AndrewPasco/me327-proj/controllerTest/controllerTest/src/BeltIMU.cpp

#include "BeltIMU.h"

BeltIMU::BeltIMU() :
    bno08x(-1),
    oldQuat{1,0,0,0}
{
    return;
}

BeltIMU::~BeltIMU(){}

// pass the quaternion you want the device to consider as
// its initial orientation, relative to lying flat (probably)
// just set to 1,0,0,0 and then orient it how you want, print the
// quaternion, and pass that
void BeltIMU::setup(Quat initialOrientation){
    initQ = Qnormalize(initialOrientation);
    oldQuat = initQ;

    if (!bno08x.begin_I2C()) {
        Serial.println("Failed to find BNO08x chip");
        return;
    }
    connected = true;
    set_reports();
    Serial.println("Reading IMU events");
}

bool BeltIMU::check_connection() {
    // re attemp connectino if not connected
    if (!connected) {
        if (!bno08x.begin_I2C()) {
            Serial.println("Failed to find BNO08x chip");
            return false;
        }
        connected = true;
    }

    // reset reports if device was reset
    if (bno08x.wasReset()) {
        Serial.print("IMU was reset, attempting to set reports ");
        justReset = true;
        bool reEnabled = set_reports();
        return reEnabled;
    }
    return true;
}

Quat BeltIMU::get_quaternion () {
    if (!connected) {
        Serial.println("IMU not connected");
        return oldQuat;
    }

    // retrieve quaternion from IMU. It will always be oriented assuming
    // initial position is board lying flat down
    sh2_SensorValue_t data;
    if (!bno08x.getSensorEvent(&data)) {
        // No new data available this loop iteration
        return oldQuat;
    }
    float qw = data.un.rotationVector.real;
    float qx = data.un.rotationVector.i;
    float qy = data.un.rotationVector.j;
    float qz = data.un.rotationVector.k;
    Quat newQuat{qw,qx,qy,qz};

    // rotate quaternion by opposite of initial orientation quaternion
    // to find quaternion relative to initial orientation
    Quat reorientedQuat = Qmultiply( newQuat, Qconj(initQ) );
    
    // if (justReset) {
    //     // Find offsetQ such that Qmultiply(reorientedQuat, offsetQ) == oldQuat
    //     // offsetQ = Qmultiply(Qconj(reorientedQuat), oldQuat)
    //     offsetQ = Qmultiply(Qconj(reorientedQuat), oldQuat);
    //     justReset = false;
    // }
    
    // Apply offset
    Quat finalQuat = Qmultiply(reorientedQuat, offsetQ);
    
    oldQuat = finalQuat;

    return finalQuat;
}

float BeltIMU::get_heading() {
    // get latest quaternion
    Quat q = get_quaternion();
    // Convert to Euler Yaw (heading)
    // using standard formula
    float siny_cosp = 2.0f * (q.w * q.z + q.x * q.y);
    float cosy_cosp = 1.0f - 2.0f * (q.y * q.y + q.z * q.z);
    float yaw_rad = atan2(siny_cosp, cosy_cosp);
    float yaw_deg = yaw_rad * 180.0f / M_PI;
    return yaw_deg;
}


/****************
 Private
*****************/
bool BeltIMU::set_reports() {
    if (!connected) {
        return false;
    }
    Serial.println("Setting desired reports");
    if (! bno08x.enableReport(SH2_GAME_ROTATION_VECTOR)) {
        Serial.println("Could not enable game vector");
        return false;
    }
    return true;
}

/****************
 Quaternion Stuff
*****************/
Quat Qmultiply(const Quat& a, const Quat& b) {
    float qw = a.w*b.w - a.x*b.x - a.y*b.y - a.z*b.z;
    float qx = a.w*b.x + a.x*b.w + a.y*b.z - a.z*b.y;
    float qy = a.w*b.y - a.x*b.z + a.y*b.w + a.z*b.x;
    float qz = a.w*b.z + a.x*b.y - a.y*b.x + a.z*b.w;
    
    Quat qnew{qw, qx, qy, qz};
    return Qnormalize(qnew);
}

Quat Qconj(const Quat& q) {
    return {q.w, -q.x, -q.y, -q.z};
}

Quat Qnormalize(Quat q) {
    float n = sqrt(q.w*q.w + q.x*q.x + q.y*q.y + q.z*q.z);
    return {q.w/n, q.x/n, q.y/n, q.z/n};
}

void printQuat(Quat q) {
    Serial.print("qw:");
    Serial.print(q.w);
    Serial.print(" qx:");
    Serial.print(q.x);
    Serial.print(" qy:");
    Serial.print(q.y);
    Serial.print(" qz:");
    Serial.print(q.z);
    Serial.println("");
}
