AndrewPasco/me327-proj/controllerTest/controllerTest/src/ThreatTracker.h

#pragma once
#include "Particle.h"
#include "HapticSignature.h"


struct Threat {
    int id = -1;
    bool active = false;
    float coords[3] = {0,0,0};
    HapticSignature signature;
};
class ThreatTracker
{
public:
    ThreatTracker();
    ~ThreatTracker(){};

    // parses the received byteString into the Threats array
    void update();

    // populates activeList with pointers to active threats
    int getActiveThreats(Threat* activeList[], int maxListSize);

    // calculates relative position of all threats and calls motor driver to
    // appropriately render positions of threats
    void render_threats(const float (&quat)[4]){};

    // callback function to pass to BLE handler
    static void rx_callback( const uint8_t* data,  
							size_t len,  
							const BlePeerDevice& peer,  
							void* context);


private:
    // used to lock thread to allow safe read/write of shared data
    Mutex dataMutex;
    
    static const int maxThreats = 10;
    Threat Threats[maxThreats];
    
    static const size_t messageBufferSize = 10;
    String byteStringBuffer[messageBufferSize];
    size_t messageCount = 0;


	void handle_rx(const uint8_t* data,  
					size_t len,  
					const BlePeerDevice& peer);
	
};
