AndrewPasco/me327-proj/controllerTest/controllerTest/src/BeltIMU.h

#pragma once
#include  "Adafruit_BNO08x_Sahagun.h"

// implementation at end of cpp file
struct Quat {
    float w, x, y, z;
};
Quat Qmultiply(const Quat& a, const Quat& b);
Quat Qconj(const Quat& q);
Quat Qnormalize(Quat q);
void printQuat(Quat q);


class BeltIMU
{
public:
    BeltIMU();
    ~BeltIMU();

    void setup(Quat initialOrientation = {1,0,0,0});

    bool check_connection();

    Quat get_quaternion ();
    float get_heading();
    
private:
    Adafruit_BNO08x bno08x;
    Quat oldQuat;
    Quat initQ;
    Quat offsetQ = {1,0,0,0};

    bool connected = false;
    bool justReset = false;

    bool set_reports();

};
