AndrewPasco/me327-proj/v_env/gui_single.py

# written by Ashlynn as the start of the GUI for the project. 
# This is a simple visualization of the user's heading and the threat location, and it sends motor commands based on the relative angle between the user and the threat. 
# The user can click to set the threat location and use the A/D keys to rotate their heading.
# This script only supports a single threat.

# runs on python 3.11 with pygame, pyserial, numpy, scipy, filterpy, bleak, bluetooth, bluez, bluez-tools

import pygame
import math
# import serial
import time
# BT imports
import asyncio
from bleak import BleakClient, BleakScanner
import threading

# ------------------
# CONFIG
# ------------------

WIDTH = 800
HEIGHT = 800

CENTER = (WIDTH // 2, HEIGHT // 2)

THREAT_X = 500
THREAT_Y = 300

user_heading_deg = 0
latest_heading = 0

NUM_MOTORS = 8
SECTOR_SIZE = 360 / NUM_MOTORS

# For serial
# ser = serial.Serial("/dev/ttyUSB0", 115200)

# For BLE
BLE_ADDRESS = "e8:9f:6d:f2:2c:08"   # MAC address of the Particle Argon
# BLE_ADDRESS = "XX:XX:XX:XX:XX:XX"  # replace with device's MAC address
# BLE_CHARACTERISTIC_UUID = "XXXXXXXX-XXXX-XXXX-XXXX-XXXXXXXXXXXX"  # replace with characteristic UUID

pygame.init()
screen = pygame.display.set_mode((WIDTH, HEIGHT))
clock = pygame.time.Clock()


def normalize_angle(angle):
    return angle % 360


def get_relative_angle():

    dx = THREAT_X - CENTER[0]
    dy = CENTER[1] - THREAT_Y

    world_angle = math.degrees(
        math.atan2(dx, dy)
    )

    relative = normalize_angle(
        world_angle - user_heading_deg
    )

    return relative


def angle_to_motor(angle):

    sector = round(
        angle / SECTOR_SIZE
    ) % NUM_MOTORS

    return sector


def send_motor_command(motor_id):

    msg = f"{motor_id}\n"

    print("TX:", msg.strip())

    # Uncomment when hardware ready
    # ser.write(msg.encode())

def handle_ble_data(sender, data):
    global latest_heading

    try:
        msg = data.decode().strip()

        # assumes "YAW,127.4" is what the BLE device sends, where 127.4 is the heading in degrees
        if "YAW" in msg:
            latest_heading = float(msg.split(",")[1])

        else:
            latest_heading = float(msg)

    except:
        pass

async def scan_for_devices():

    print("Scanning for BLE devices...")

    devices = await BleakScanner.discover(timeout=5.0)

    print("\nFound devices:")

    for d in devices:
        print(f"Name: {d.name}, Address: {d.address}")

async def ble_loop():
    global latest_heading

    async with BleakClient(BLE_ADDRESS) as client:
        print("Connected to IMU BLE")

        await client.start_notify(BLE_CHARACTERISTIC_UUID, handle_ble_data)

        while True:
            await asyncio.sleep(0.01)

# running in a background thread
def start_ble():

    async def runner():

        await scan_for_devices()

        # STOP HERE for now
        # later you will connect

    asyncio.run(runner())

# ble_thread = threading.Thread(target=start_ble, daemon=True)
# ble_thread.start()

start_ble()

running = True

while running:

    for event in pygame.event.get():

        if event.type == pygame.QUIT:
            running = False

        if event.type == pygame.MOUSEBUTTONDOWN:

            THREAT_X, THREAT_Y = event.pos

    # replace the keys with the following line to use BLE heading instead of keyboard input
    # user_heading_deg = latest_heading

    # ------- KEYBOARD ------------
    keys = pygame.key.get_pressed()

    if keys[pygame.K_a]:
        user_heading_deg += 2

    if keys[pygame.K_d]:
        user_heading_deg -= 2
    # ----------- KEYBOARD ----------

    relative_angle = get_relative_angle()

    motor = angle_to_motor(
        relative_angle
    )

    send_motor_command(motor)

    # ------------------
    # DRAW
    # ------------------

    screen.fill((20, 20, 20))

    # user
    pygame.draw.circle(
        screen,
        (255,255,255),
        CENTER,
        20
    )

    # heading arrow
    hx = CENTER[0] + 60*math.sin(
        math.radians(
            user_heading_deg
        )
    )

    hy = CENTER[1] - 60*math.cos(
        math.radians(
            user_heading_deg
        )
    )

    pygame.draw.line(
        screen,
        (0,255,0),
        CENTER,
        (hx, hy),
        4
    )

    # threat
    pygame.draw.circle(
        screen,
        (255,0,0),
        (THREAT_X, THREAT_Y),
        10
    )

    pygame.display.flip()

    clock.tick(30)

pygame.quit()
